apos/rapid-bulky-wshc-by-apos/media/ESP32-30pin-BO1-ESP32_compact_breakout_and ESP32.jpg

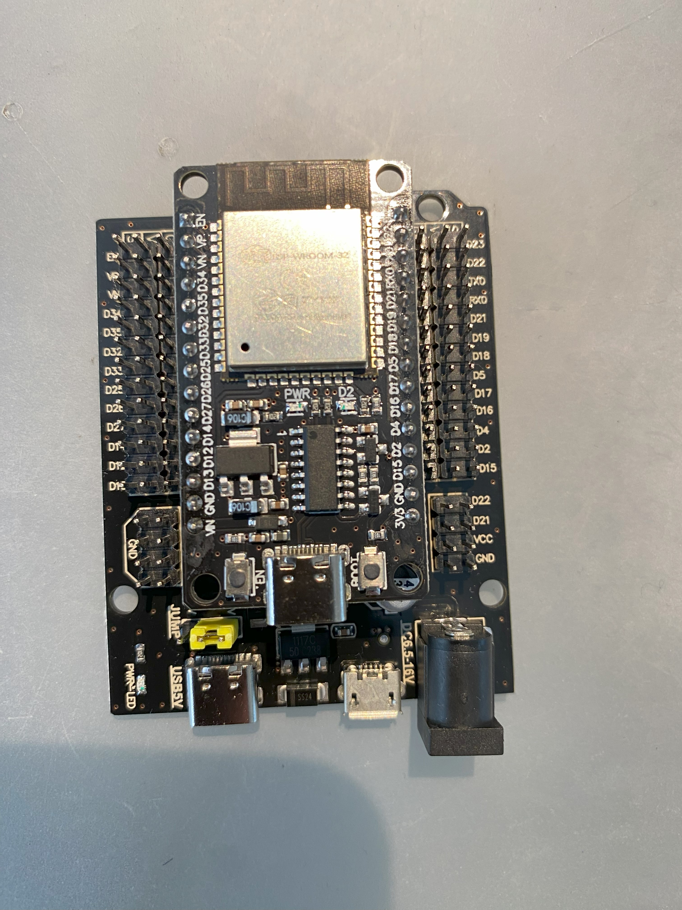
media/ESP32-30pin-BO1-ESP32_compact_breakout_and ESP32.jpg
