apos/rapid-bulky-wshc-by-apos/media/ESP32-30pin-BO1-Prototype_Joystickboard_and_1,3_OLED_01.jpg

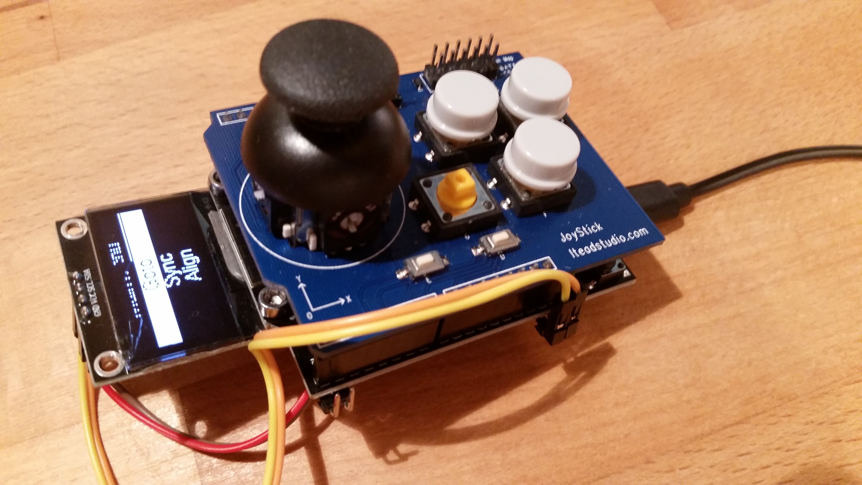
media/ESP32-30pin-BO1-Prototype_Joystickboard_and_1,3_OLED_01.jpg
