apos/rapid-bulky-wshc-by-apos/media/ESP32_38pin_left_layout_comparison.jpg

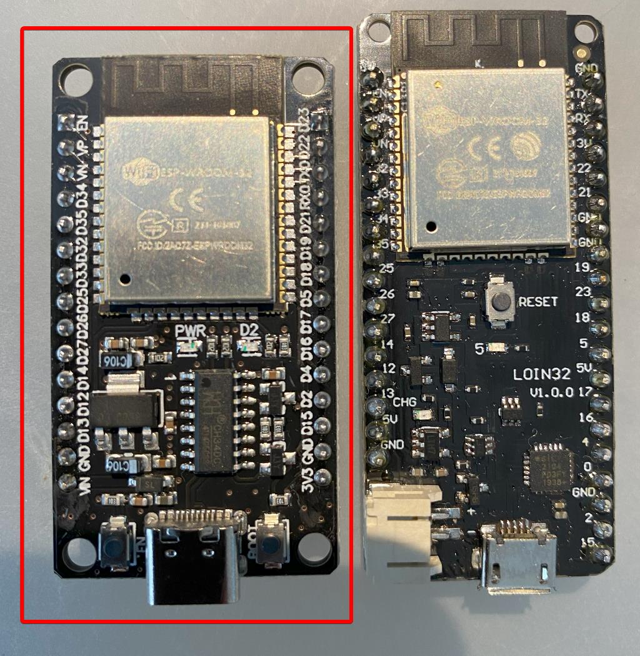
media/ESP32_38pin_left_layout_comparison.jpg
