apos/rapid-bulky-wshc-by-apos/media/ESP32_ITEAD_02.jpg

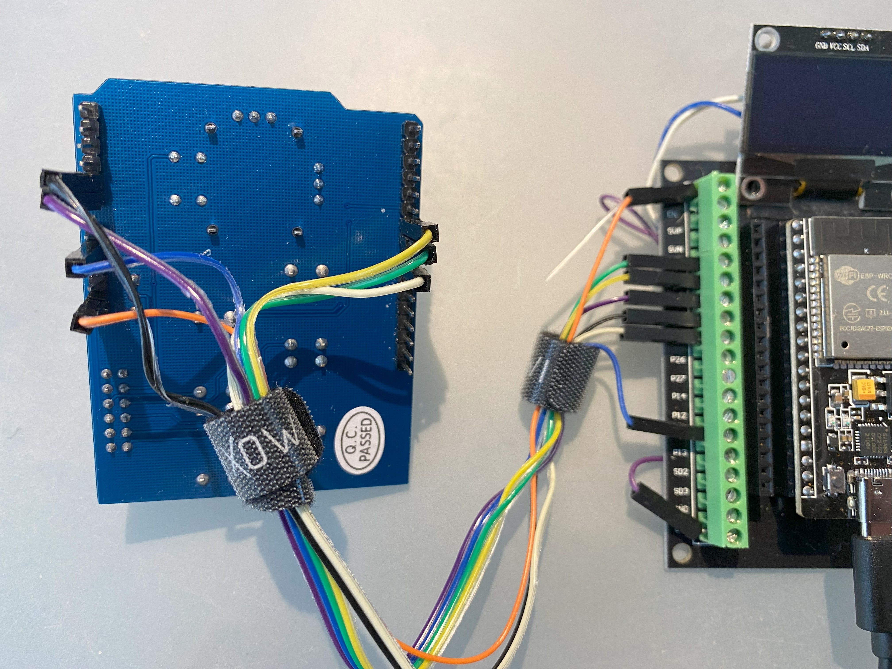
media/ESP32_ITEAD_02.jpg
