apos/rapid-bulky-wshc-by-apos/media/ESPDUINO-32/ESPDUINO-32_pinOut-R32-compressor.png

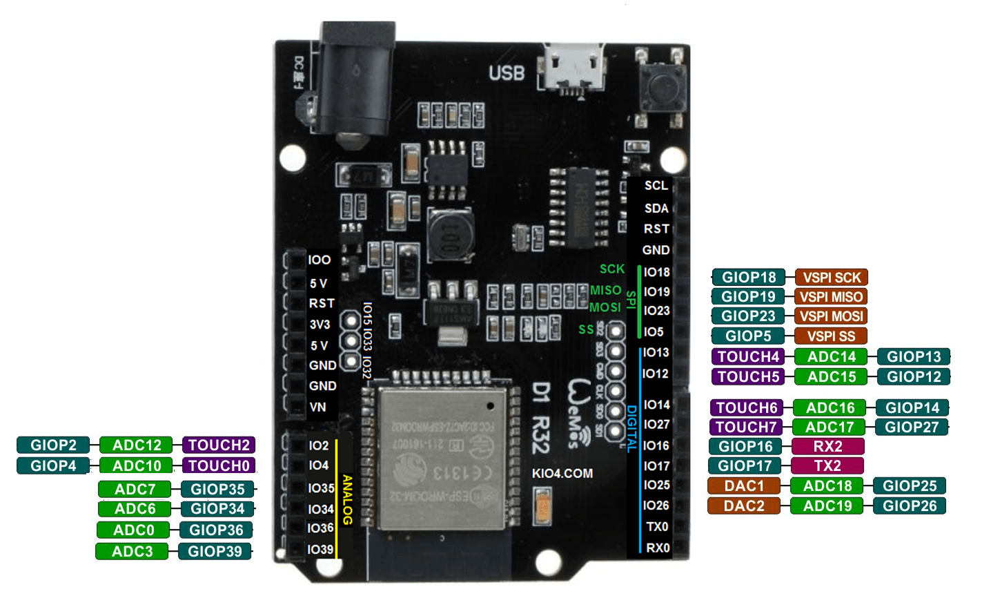
media/ESPDUINO-32/ESPDUINO-32_pinOut-R32-compressor.png
