apos/rapid-bulky-wshc-by-apos/media/OLED 2,42/SPI/OLED_2_42_inch_dimore_03.jpg

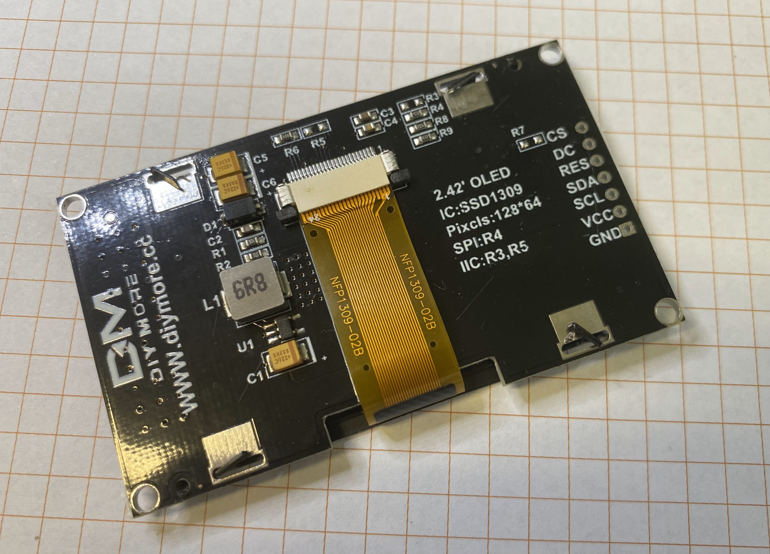
media/OLED 2,42/SPI/OLED_2_42_inch_dimore_03.jpg
