apos/rapid-bulky-wshc-by-apos/media/OLED 2,42/SPI/OLED_2_42_inch_dyimore_change_SPI_to_IIC_welding_restors.png

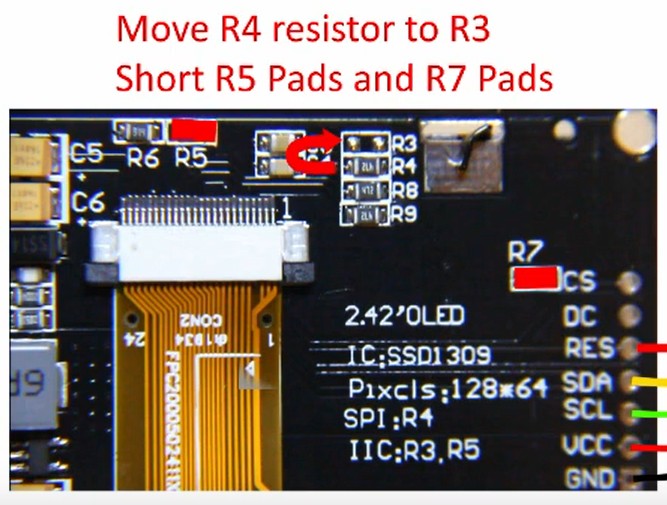
media/OLED 2,42/SPI/OLED_2_42_inch_dyimore_change_SPI_to_IIC_welding_restors.png
