apos/rapid-bulky-wshc-by-apos/media/V01a_final.png

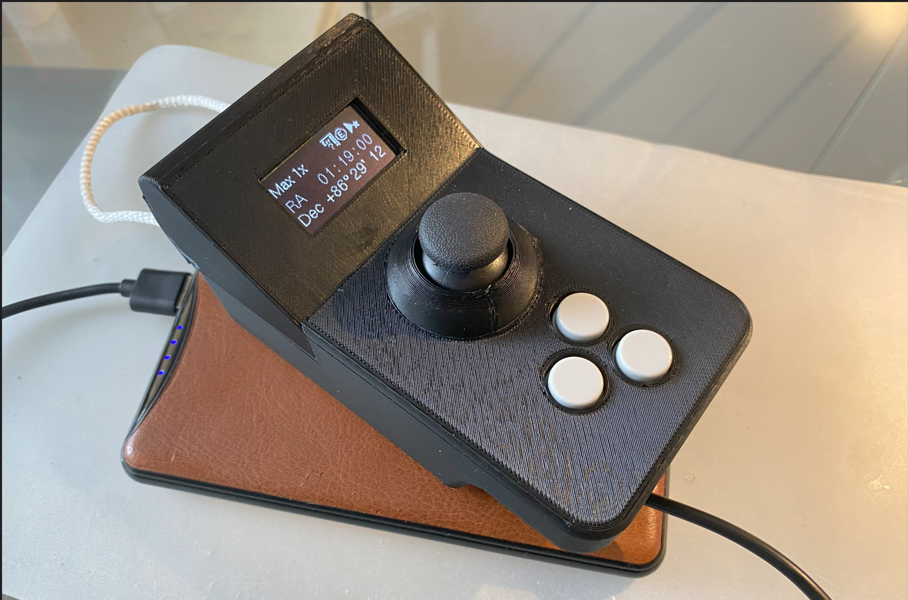
media/V01a_final.png
