apos/rapid-bulky-wshc-by-apos/media/rapid_bulky_wSHC_V01_BOM_a.jpg

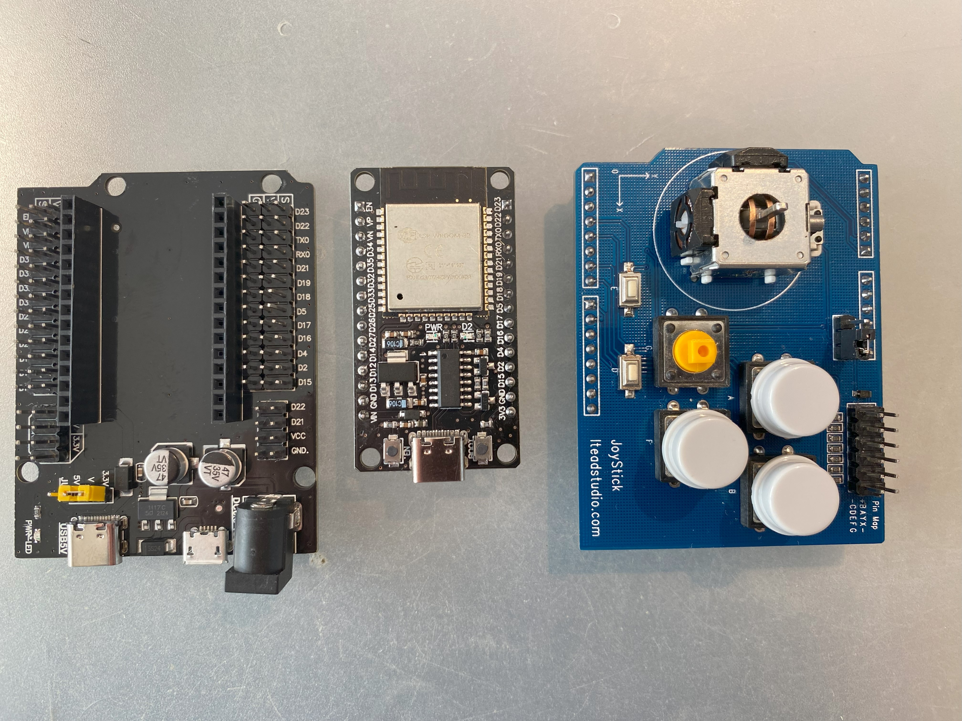
media/rapid_bulky_wSHC_V01_BOM_a.jpg
