apos/rapid-bulky-wshc-by-apos/media/rapid_bulky_wSHC_V01_BOM_Overview.jpg

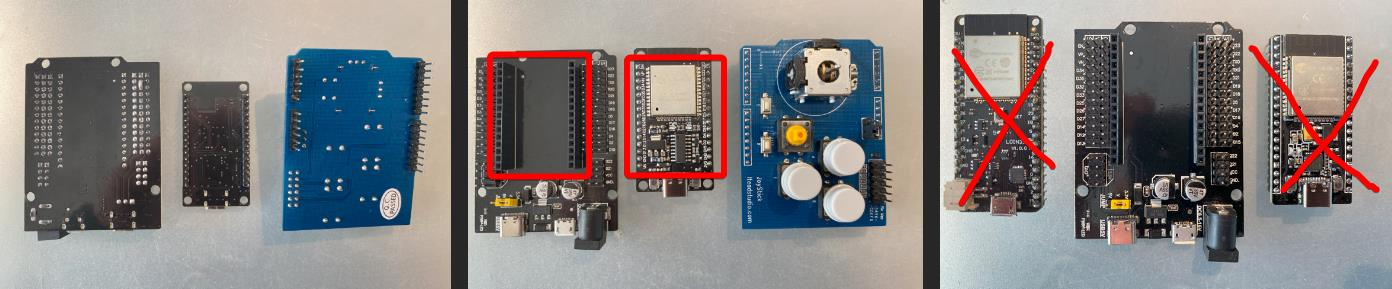
media/rapid_bulky_wSHC_V01_BOM_Overview.jpg
