apos/rapid-bulky-wshc-by-apos/3d/V_all/OLED 1,3.3mf

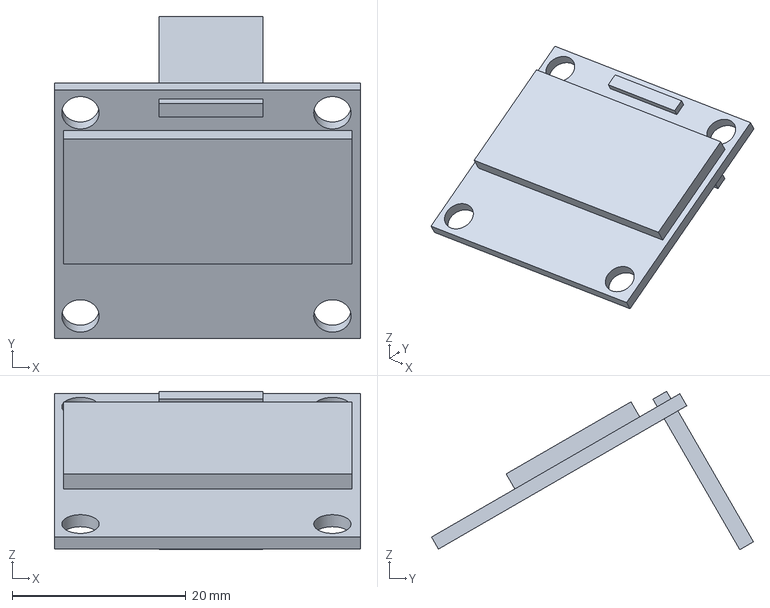
[picture p42: CAD file, 2026-01-27]
3d/V_all/OLED 1,3.3mf
35.2 x 37.1 x 18.2 mm
