apos/rapid-bulky-wshc-by-apos/3d/V_all/Base pins breakout board standard.3mf

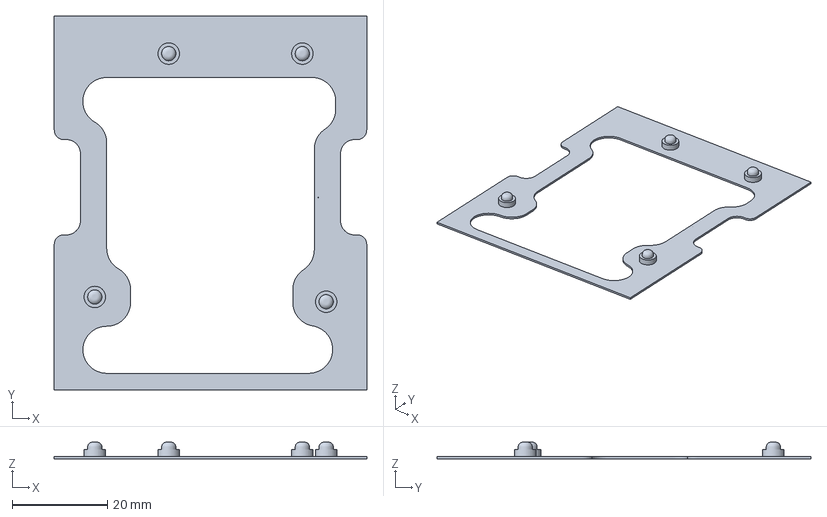
[picture p43: CAD file, 2026-01-27]
3d/V_all/Base pins breakout board standard.3mf
65.5 x 78.4 x 3.50 mm
