apos/rapid-bulky-wshc-by-apos/3d/V_all/Base front cap closed.3mf

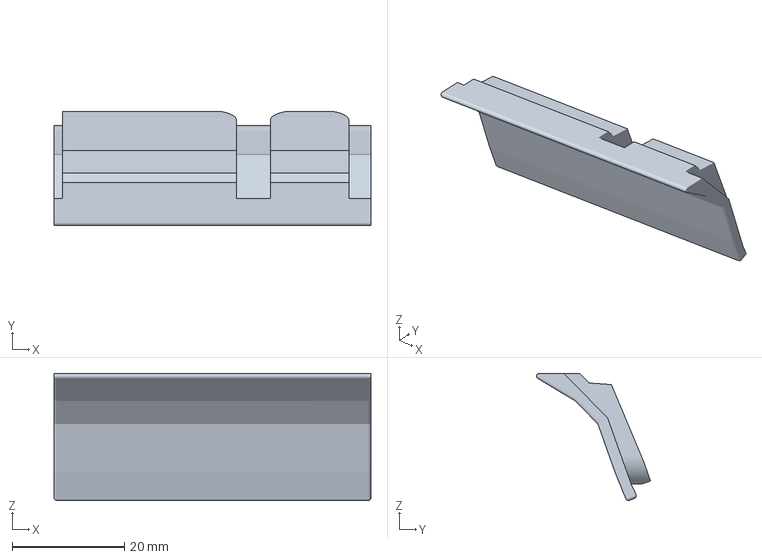
[picture p44: CAD file, 2026-01-27]
3d/V_all/Base front cap closed.3mf
56.5 x 20.3 x 22.7 mm
