apos/rapid-bulky-wshc-by-apos/3d/V_all/OLED 2,42 Display back.3mf

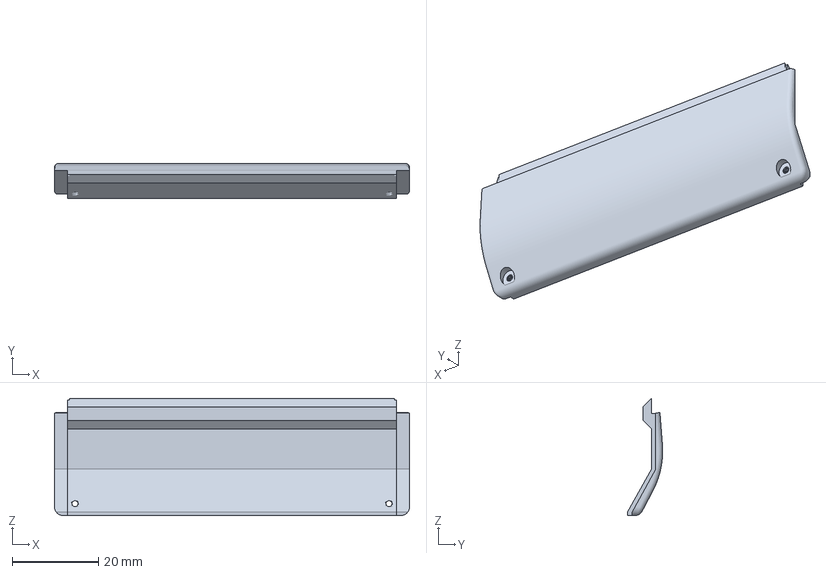
[picture p45: CAD file, 2026-01-27]
3d/V_all/OLED 2,42 Display back.3mf
82.5 x 8.23 x 27.2 mm
